wjdready/migo/sdk/lv_examples/src/lv_ex_style/lv_ex_style_1.png

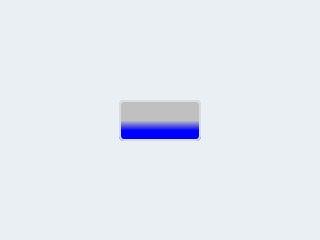
sdk/lv_examples/src/lv_ex_style/lv_ex_style_1.png
