wjdready/migo/sdk/lv_examples/src/lv_ex_widgets/lv_ex_gauge/lv_ex_gauge_2.png

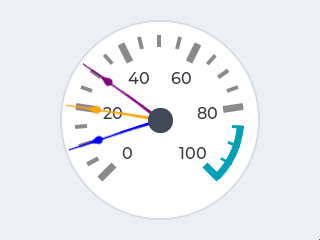
sdk/lv_examples/src/lv_ex_widgets/lv_ex_gauge/lv_ex_gauge_2.png
