wjdready/migo/sdk/lv_examples/src/lv_ex_widgets/lv_ex_spinner/lv_ex_spinner_1.png

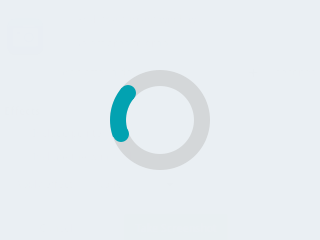
sdk/lv_examples/src/lv_ex_widgets/lv_ex_spinner/lv_ex_spinner_1.png
