wjdready/migo/sdk/lv_examples/src/lv_ex_widgets/lv_ex_textarea/lv_ex_textarea_3.png

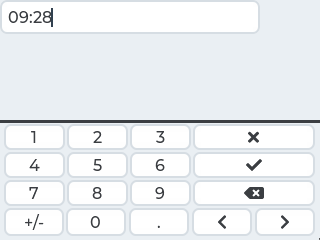
sdk/lv_examples/src/lv_ex_widgets/lv_ex_textarea/lv_ex_textarea_3.png
